priyaapatel2004/BloomX/code/codeflowchart.png

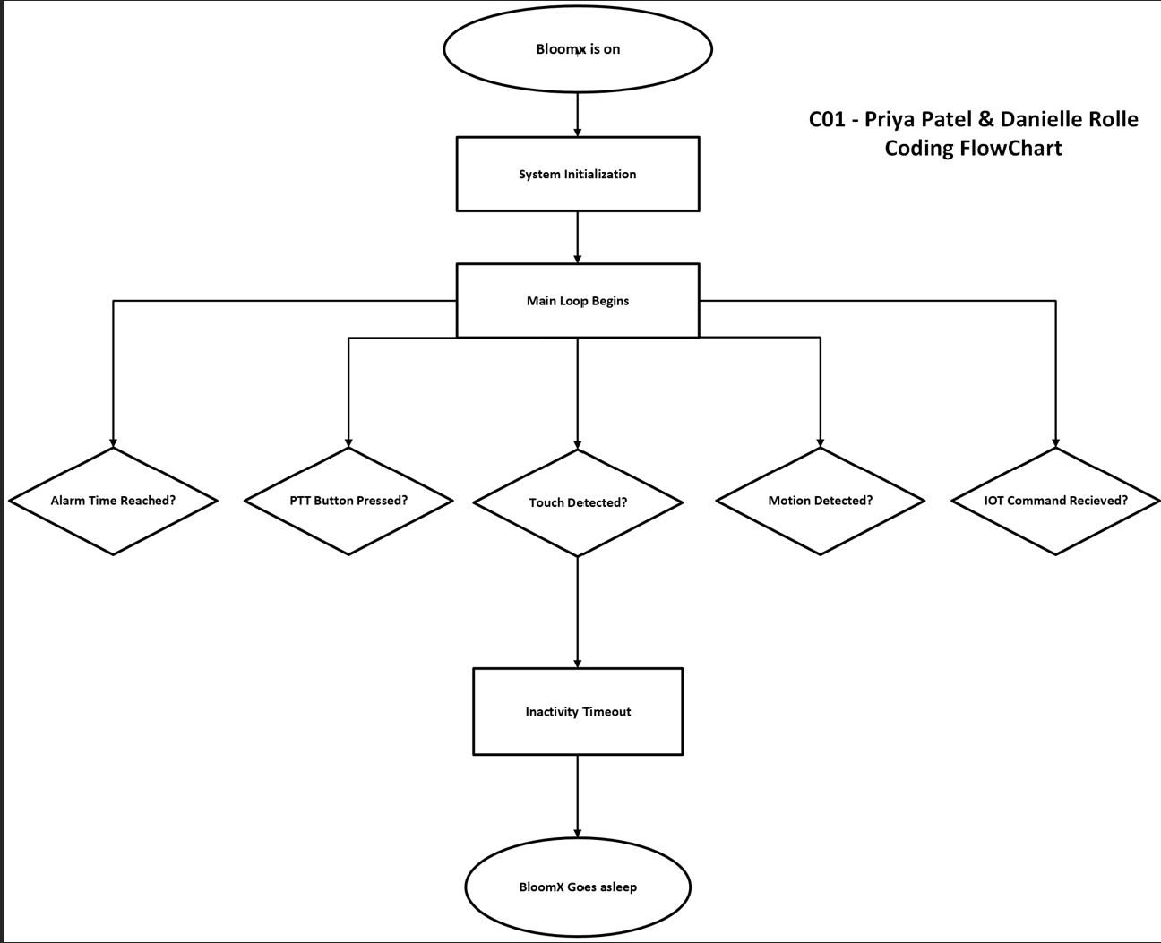
code/codeflowchart.png
