priyaapatel2004/BloomX/Diagrams/IOT/alarmstab2.png

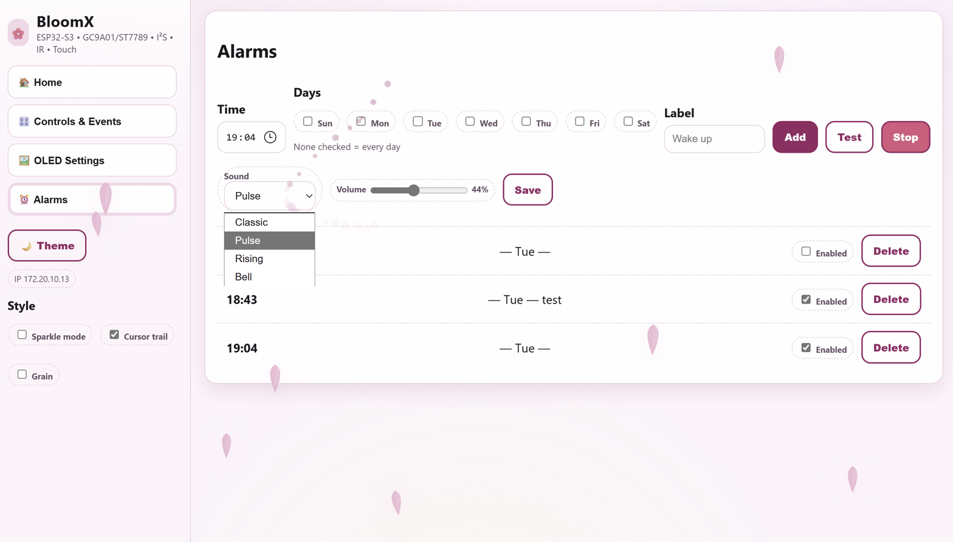
Diagrams/IOT/alarmstab2.png
