priyaapatel2004/BloomX/Diagrams/IOT/alarmstab.png

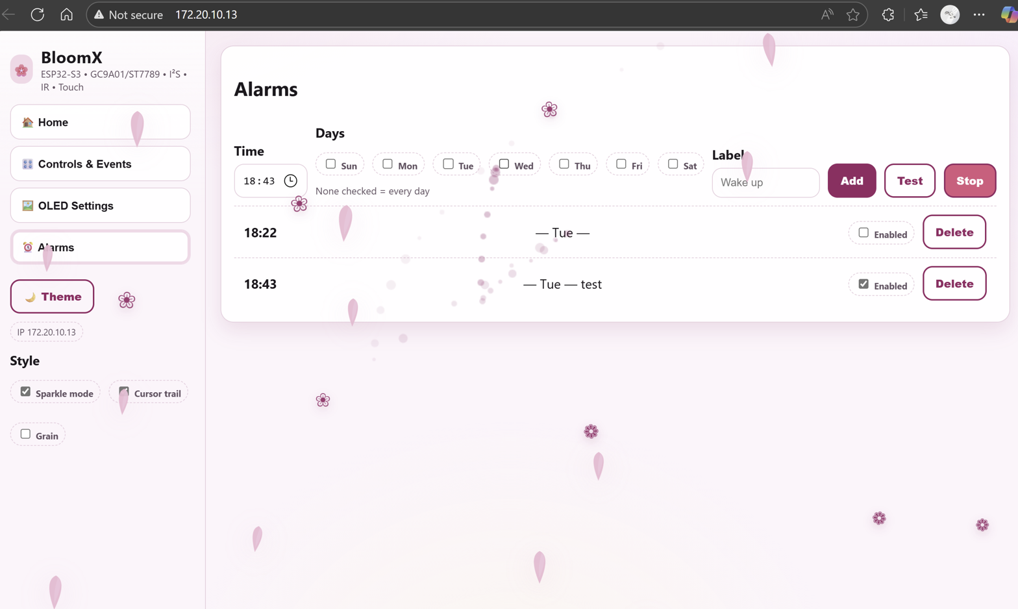
Diagrams/IOT/alarmstab.png
