priyaapatel2004/BloomX/Diagrams/IOT/controlstab.jpeg

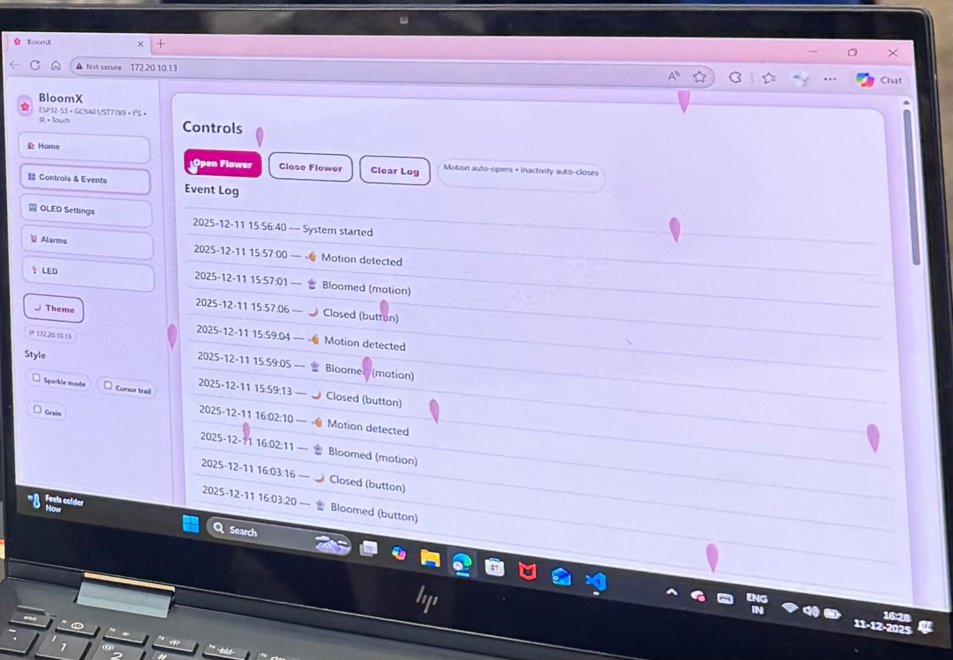
Diagrams/IOT/controlstab.jpeg
