priyaapatel2004/BloomX/Diagrams/IOT/darkmode.png

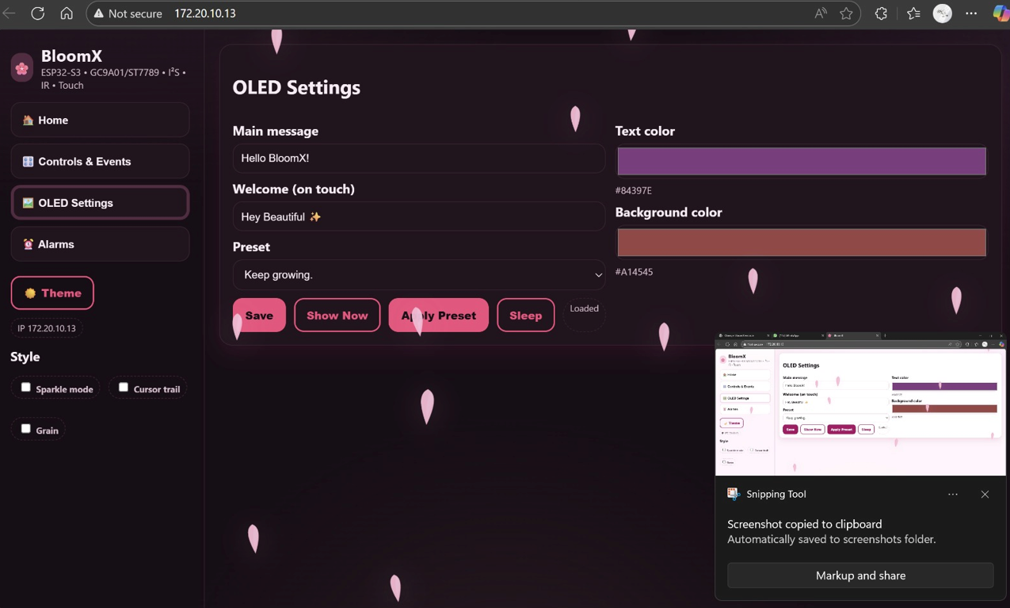
Diagrams/IOT/darkmode.png
