priyaapatel2004/BloomX/Diagrams/IOT/LEDstrips2.png

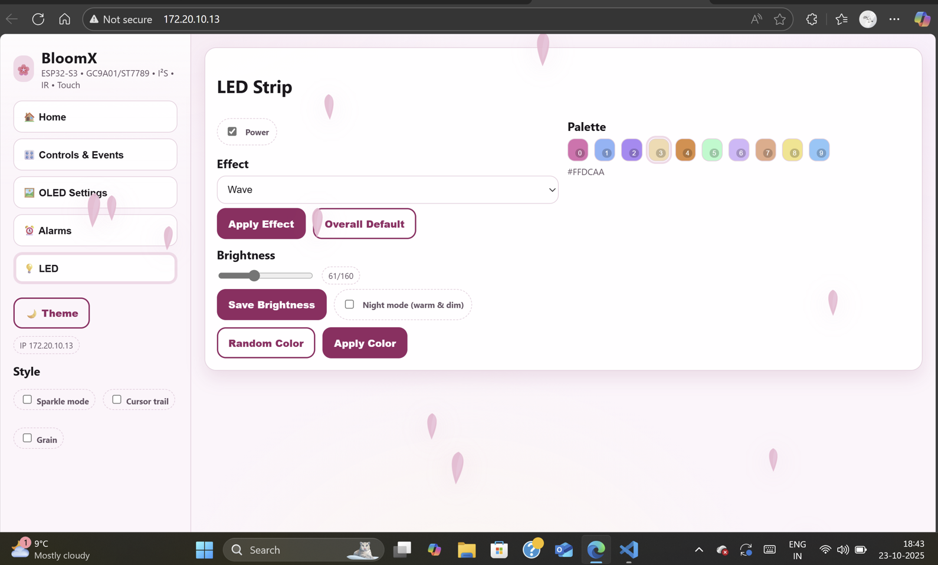
Diagrams/IOT/LEDstrips2.png
