priyaapatel2004/BloomX/Diagrams/IOT/LEDstrips.png

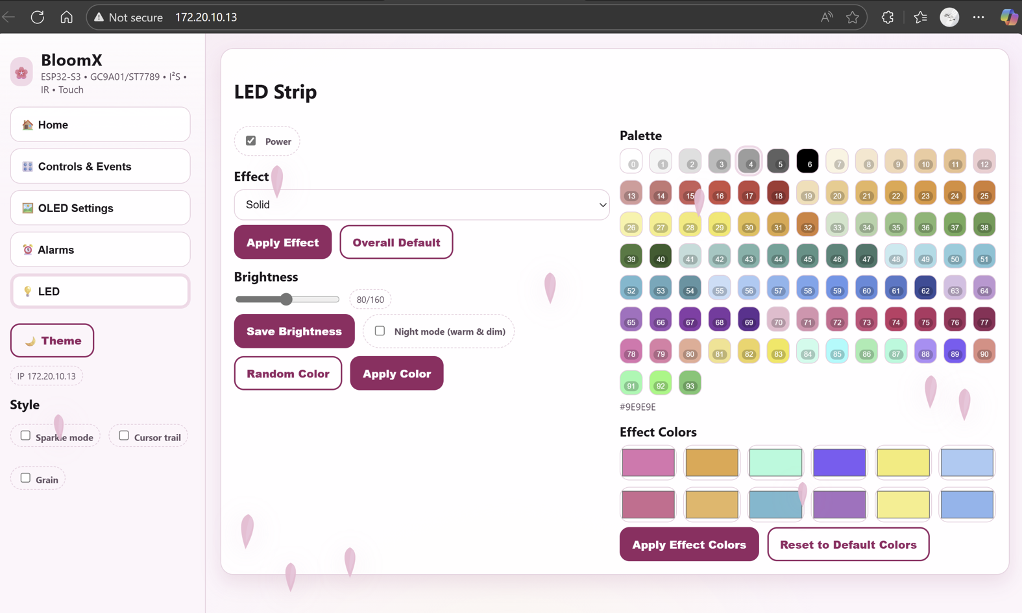
Diagrams/IOT/LEDstrips.png
