priyaapatel2004/BloomX/Diagrams/IOT/musictab2.png

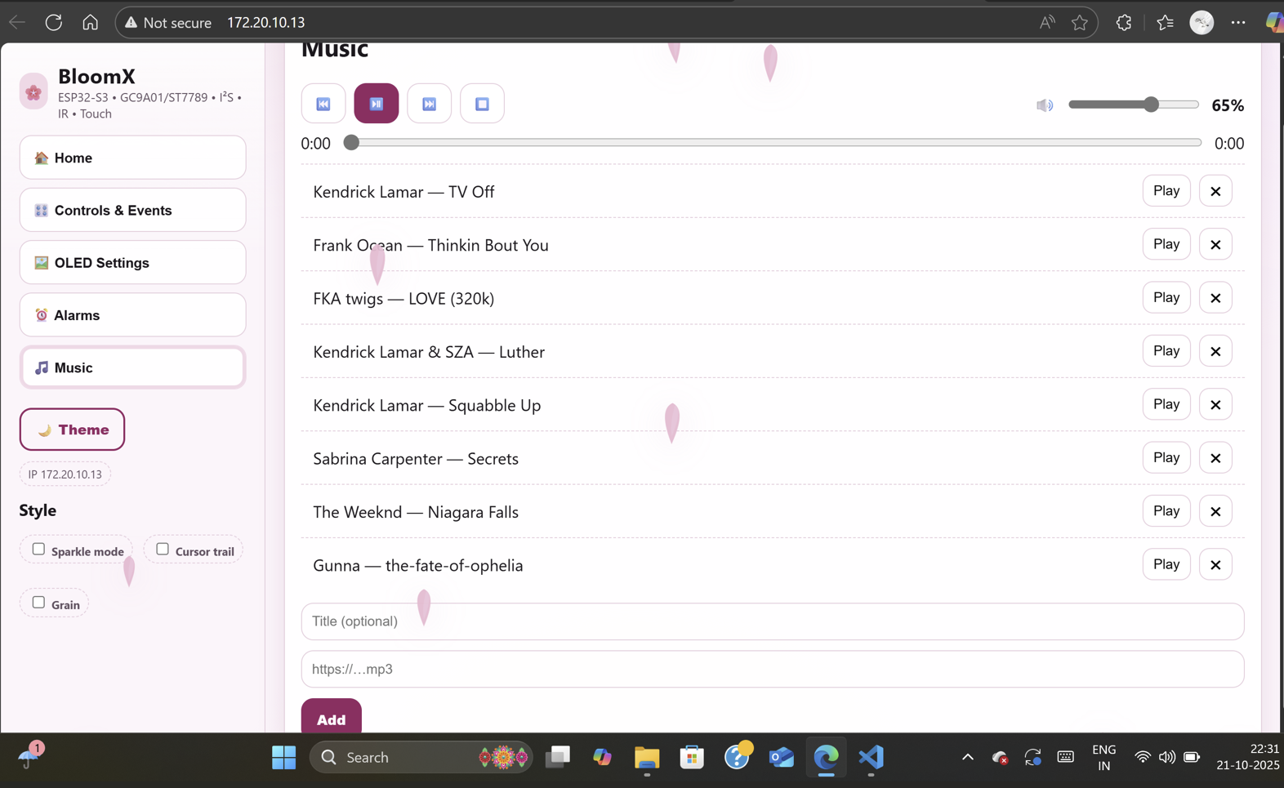
Diagrams/IOT/musictab2.png
