priyaapatel2004/BloomX/Diagrams/IOT/musictab.png

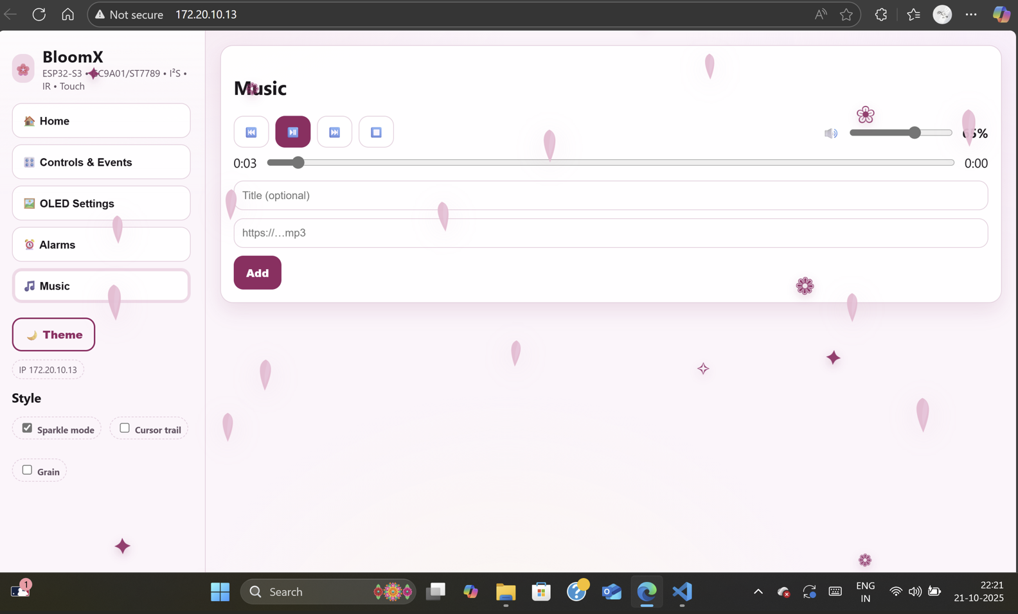
Diagrams/IOT/musictab.png
