priyaapatel2004/BloomX/Diagrams/IOT/oled.jpeg

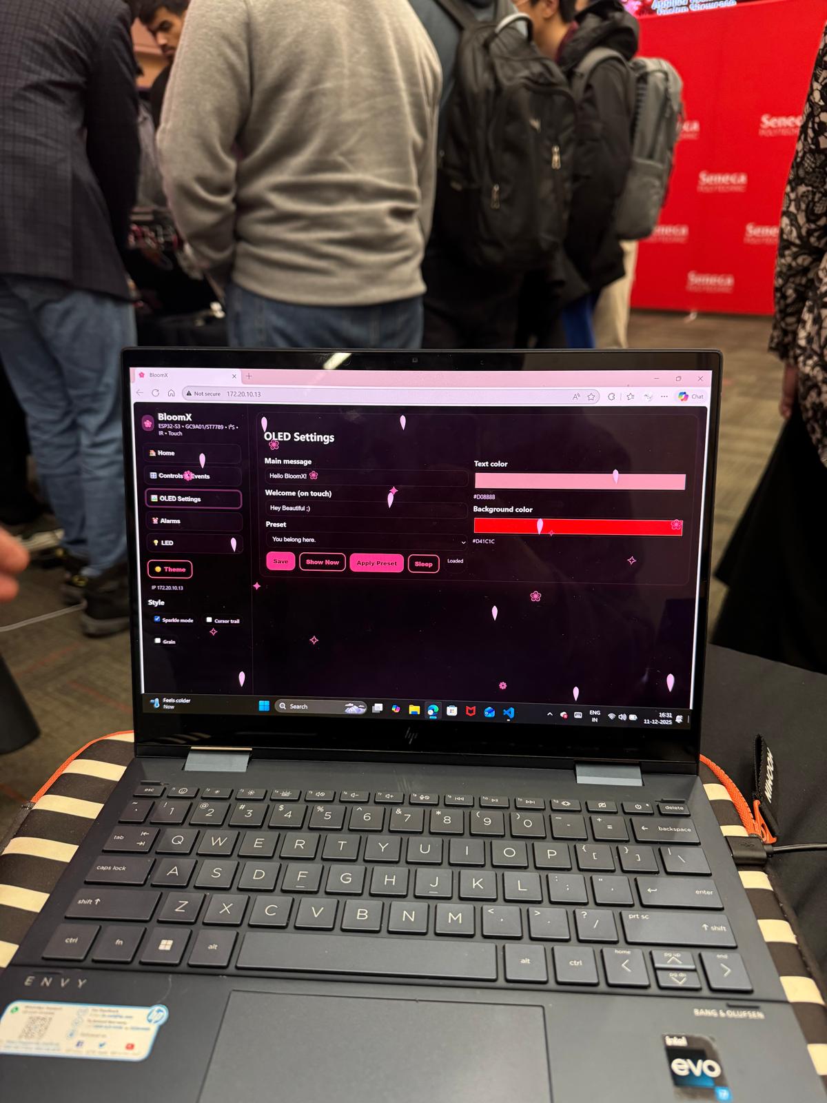
Diagrams/IOT/oled.jpeg
