priyaapatel2004/BloomX/Diagrams/IOT/oledtab.png

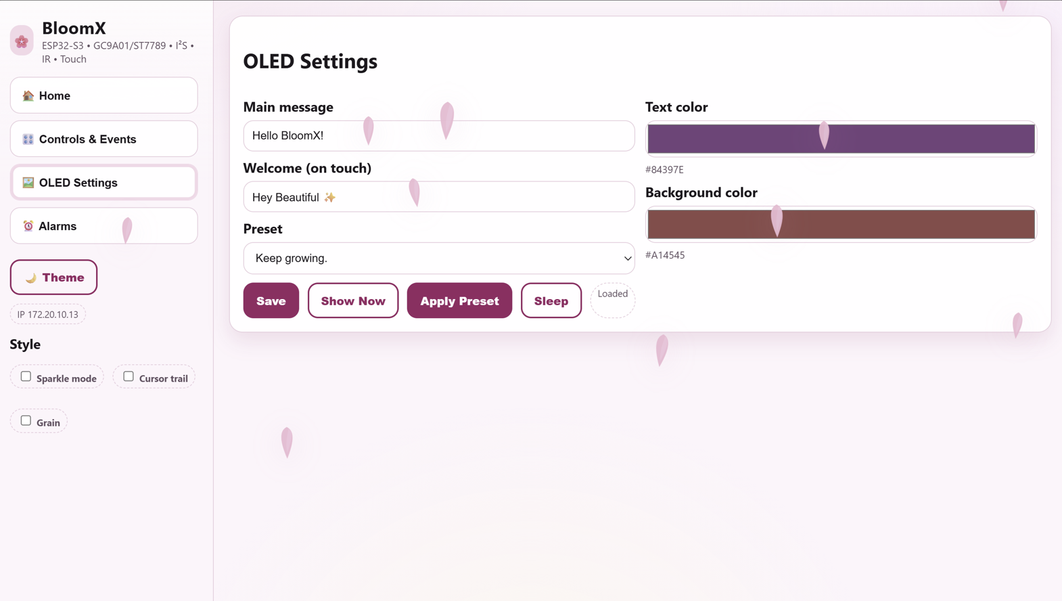
Diagrams/IOT/oledtab.png
