priyaapatel2004/BloomX/Diagrams/IOT/welcometab.jpeg

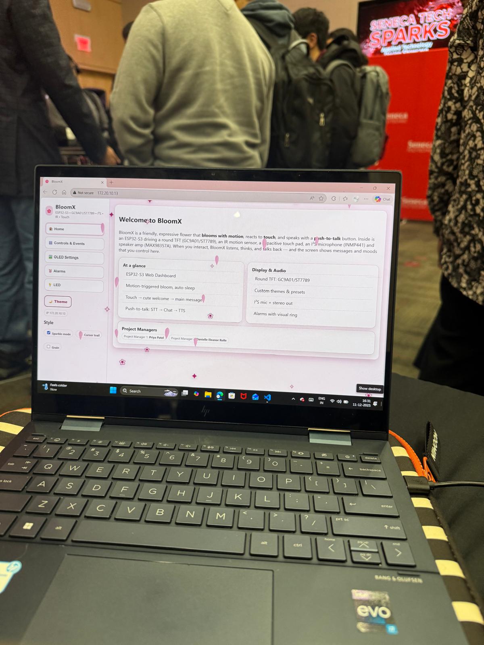
Diagrams/IOT/welcometab.jpeg
