priyaapatel2004/BloomX/Diagrams/PCB/breadboard.jpeg

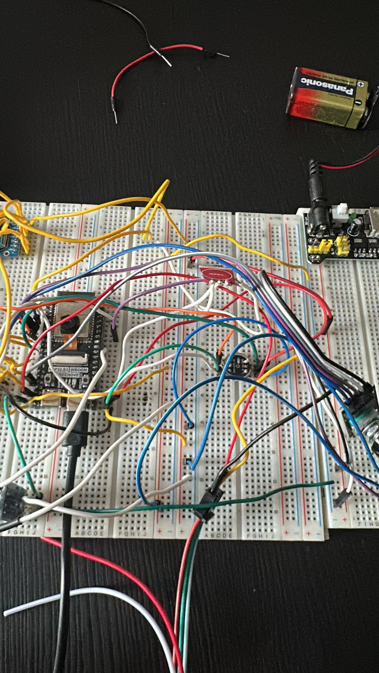
Diagrams/PCB/breadboard.jpeg
