priyaapatel2004/BloomX/Diagrams/PCB/PCB.jpeg

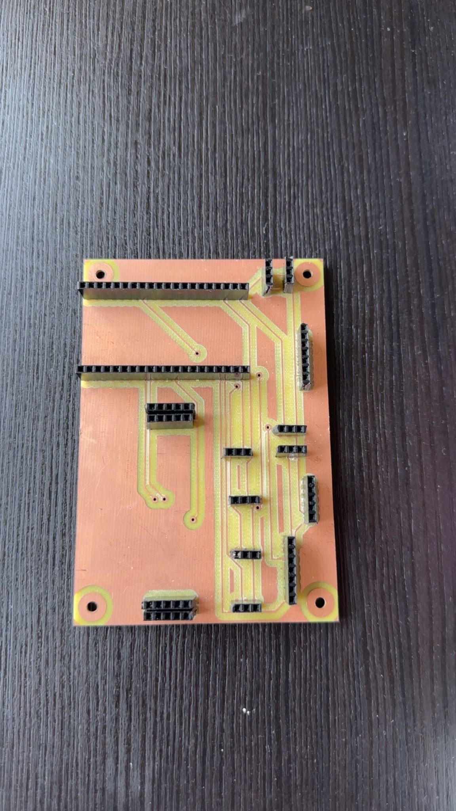
Diagrams/PCB/PCB.jpeg
