priyaapatel2004/BloomX/Images/2.jpeg

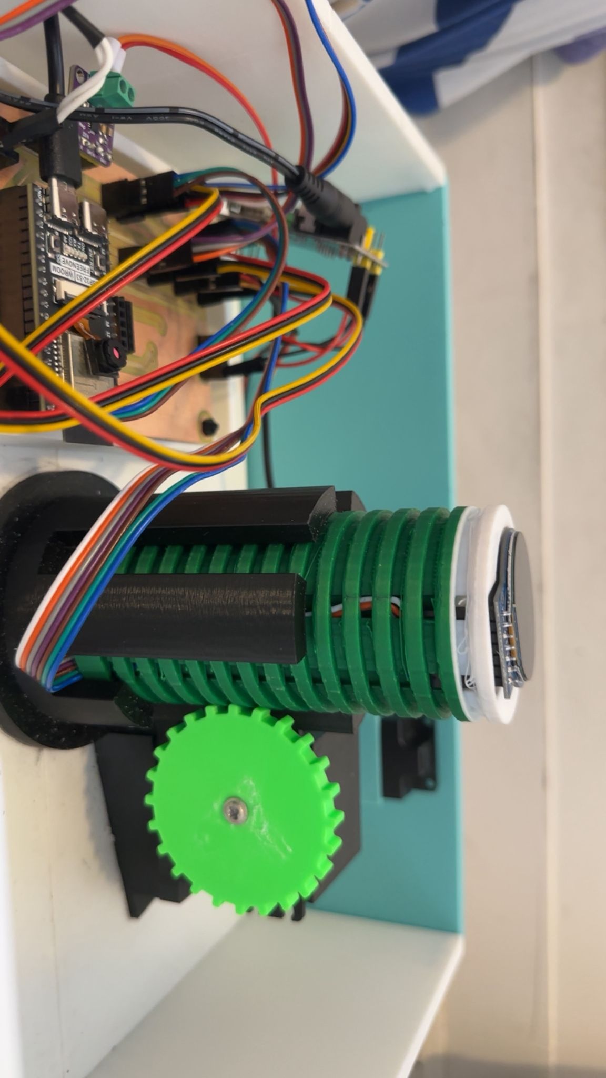
Images/2.jpeg
