priyaapatel2004/BloomX/Images/4.jpeg

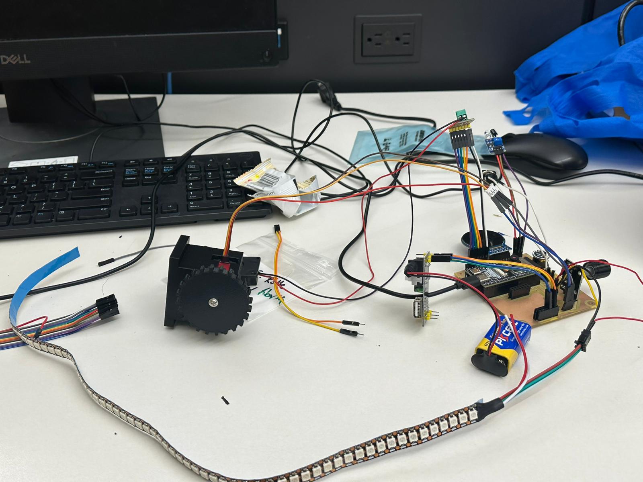
Images/4.jpeg
