priyaapatel2004/BloomX/Images/5.jpeg

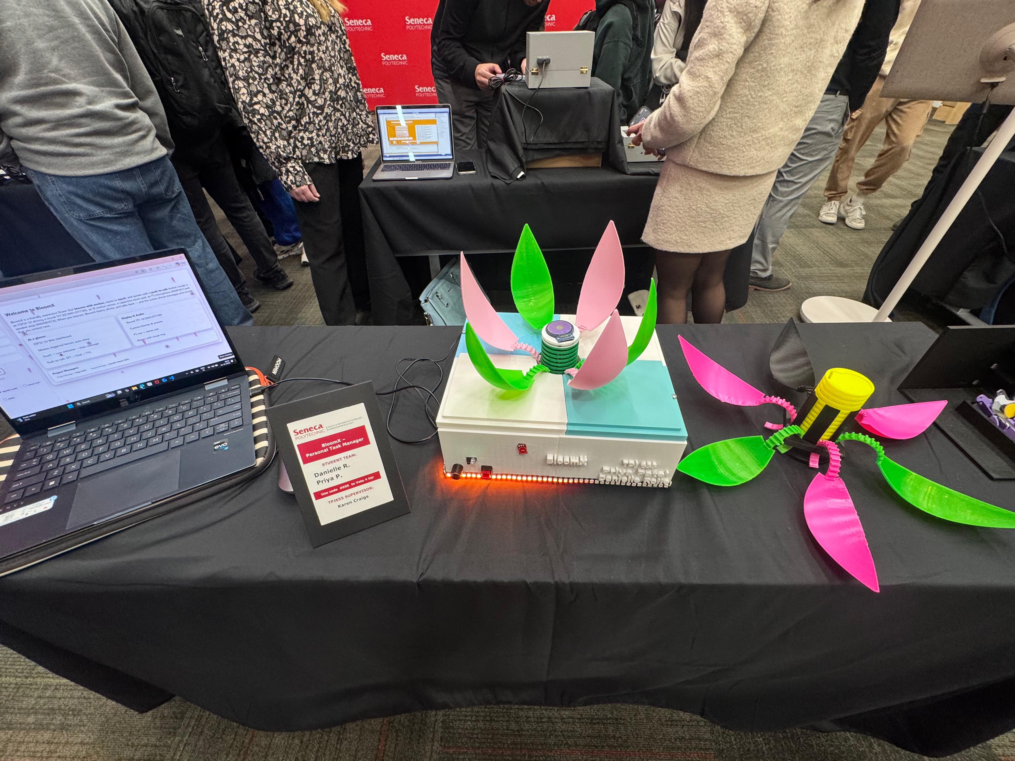
Images/5.jpeg
