priyaapatel2004/BloomX/Images/6.jpeg

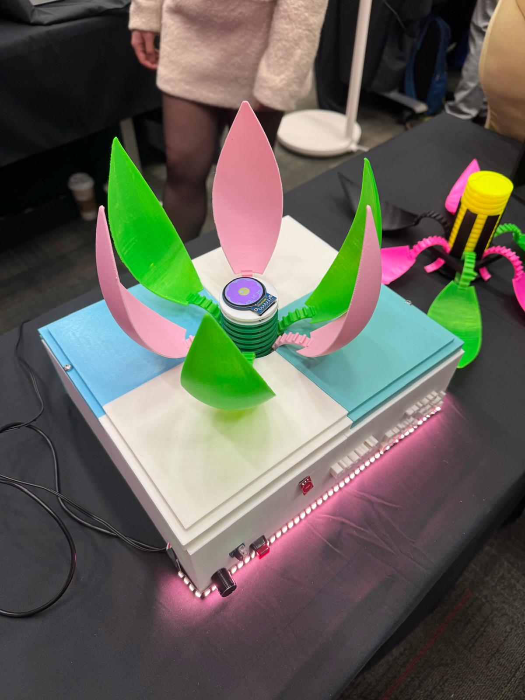
Images/6.jpeg
