priyaapatel2004/BloomX/Images/7.jpeg

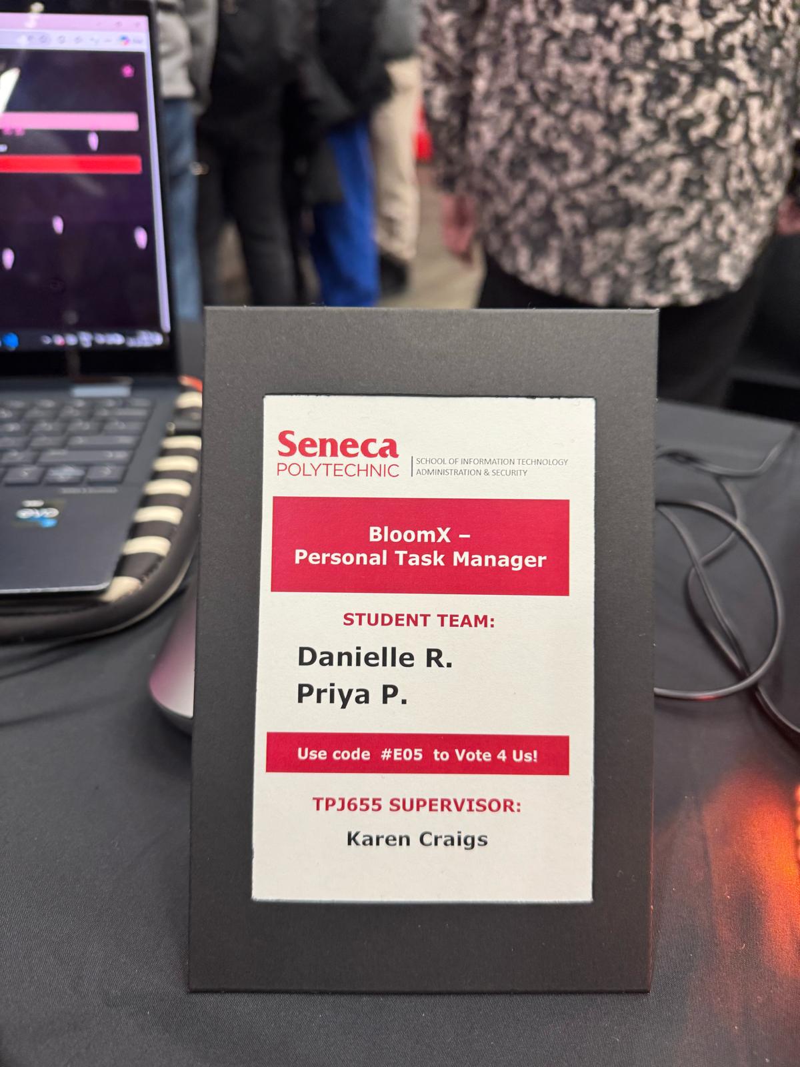
Images/7.jpeg
