priyaapatel2004/BloomX/Images/8.jpeg

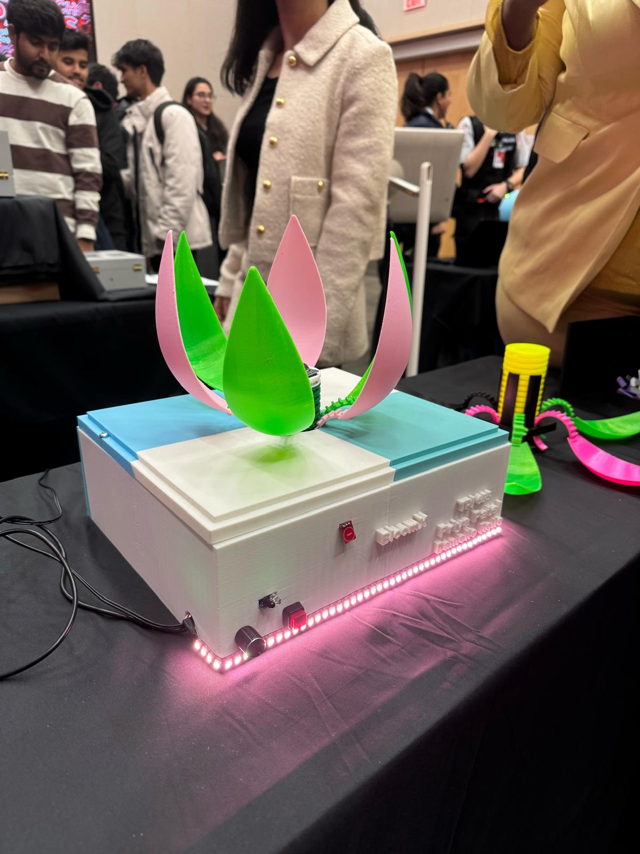
Images/8.jpeg
