priyaapatel2004/BloomX/Images/9.jpeg

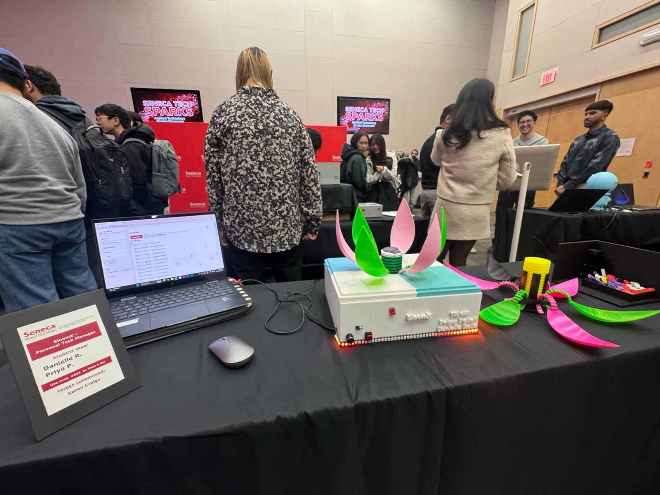
Images/9.jpeg
