priyaapatel2004/BloomX/Images/10.jpeg

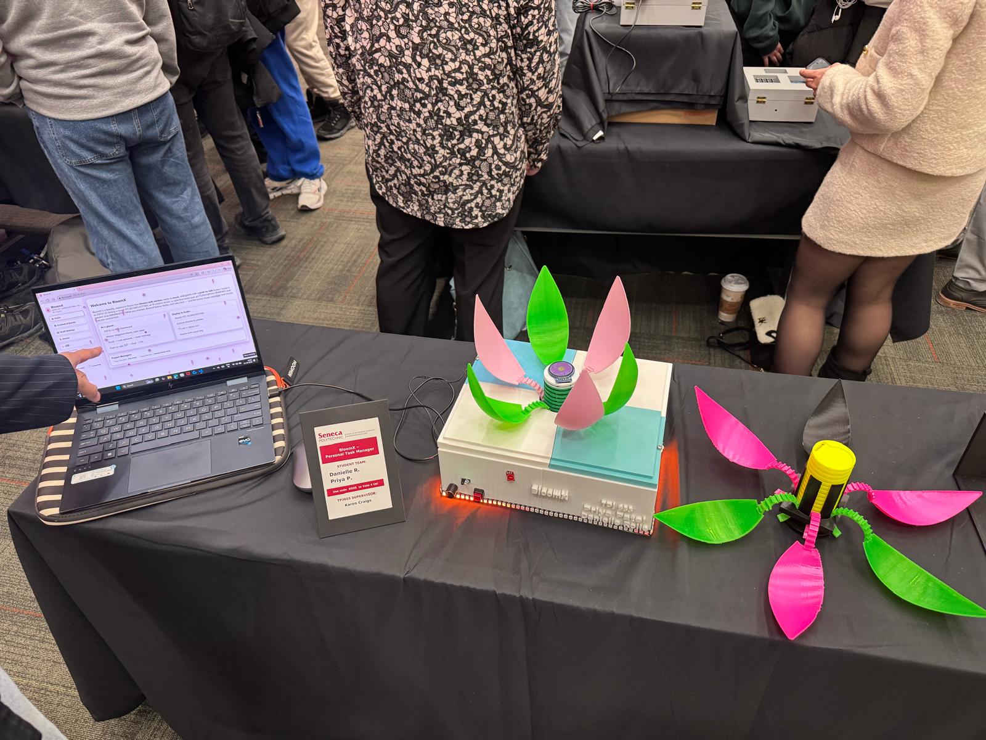
Images/10.jpeg
